Kiname/vapemacerator-mk1/SolidWorks/flame.jpg

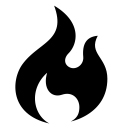
SolidWorks/flame.jpg
