Kiname/vapemacerator-mk1/SolidWorks/soporte-50ml-35mm.SLDPRT

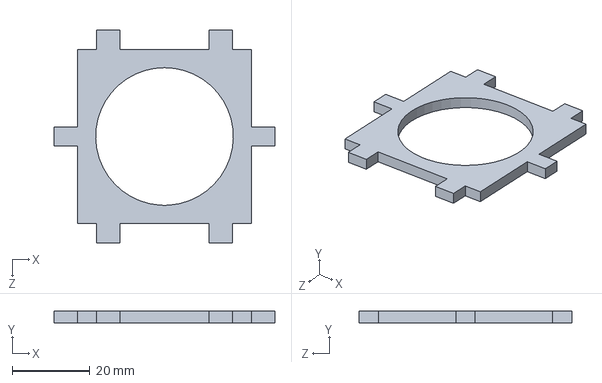
[picture p18: CAD file, 2015-08-10]
SolidWorks/soporte-50ml-35mm.SLDPRT
57.0 x 3.00 x 55.0 mm
