Kiname/vapemacerator-mk1/SolidWorks/base-back.SLDPRT

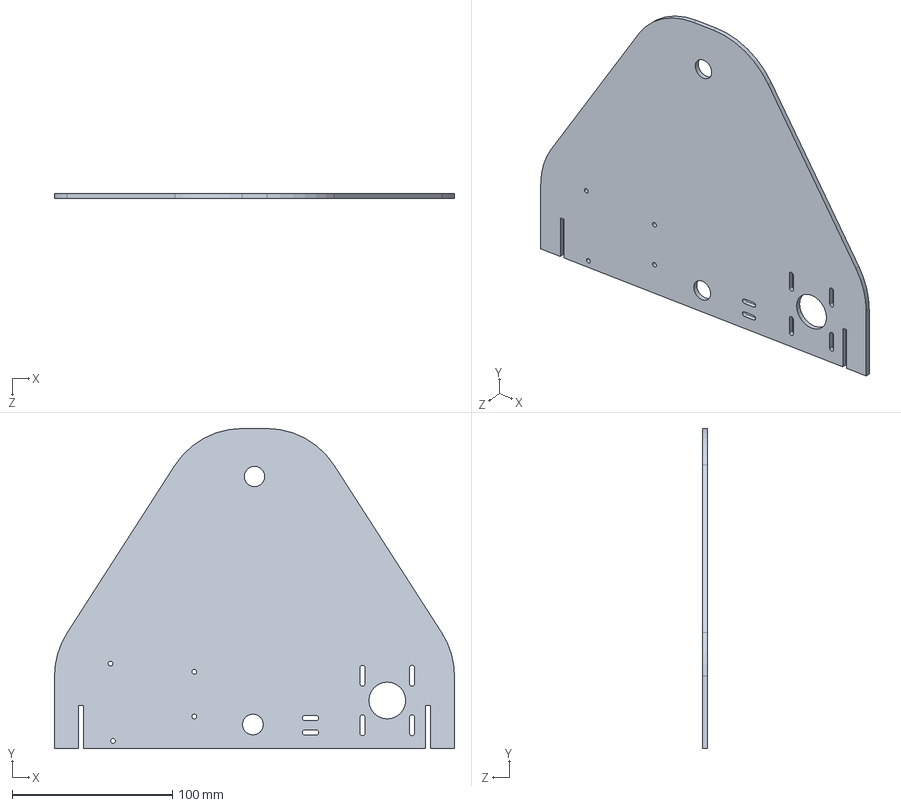
[picture p19: CAD file, 2015-08-10]
SolidWorks/base-back.SLDPRT
250.0 x 200.0 x 3.00 mm
