Kiname/vapemacerator-mk1/SolidWorks/acople.SLDPRT

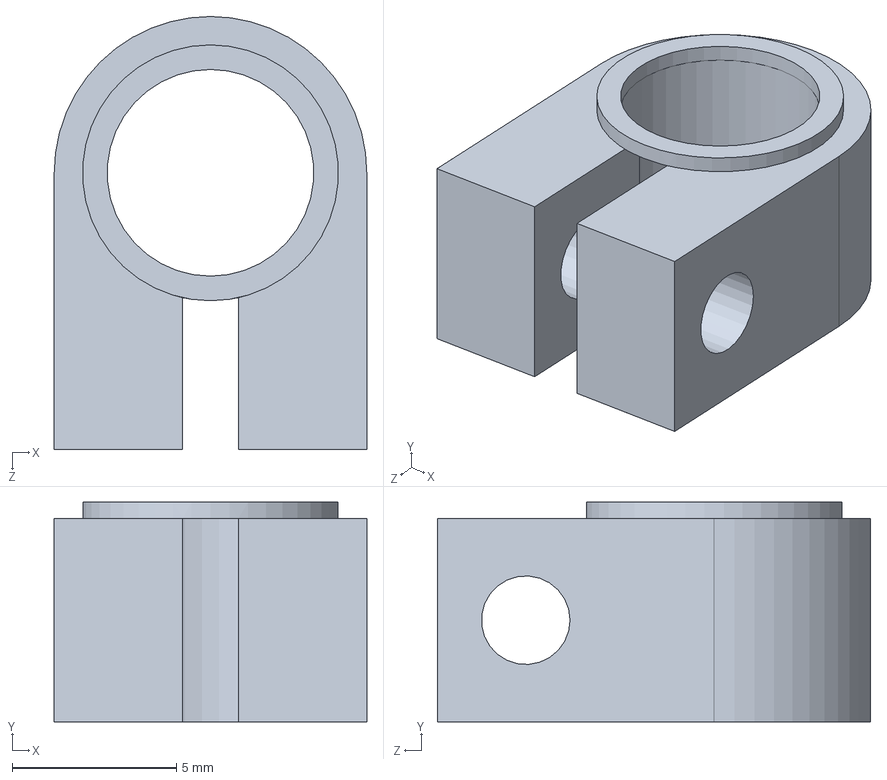
[picture p20: CAD file, 2015-08-10]
SolidWorks/acople.SLDPRT
9.53 x 6.70 x 13.2 mm
