Kiname/vapemacerator-mk1/SolidWorks/serial-lcd.SLDPRT

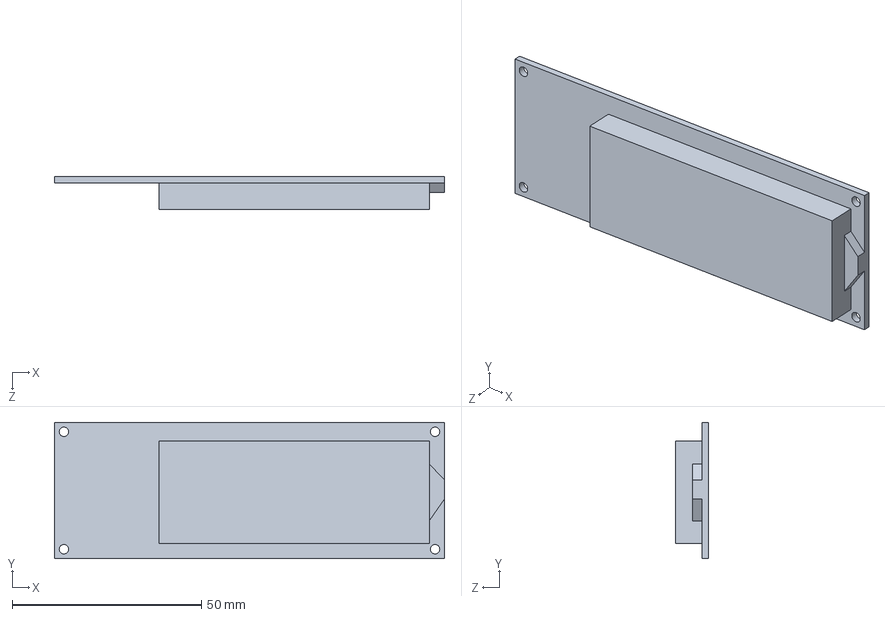
[picture p21: CAD file, 2015-08-10]
SolidWorks/serial-lcd.SLDPRT
103.0 x 36.0 x 8.75 mm
