Kiname/vapemacerator-mk1/SolidWorks/stepper-motor.sldprt

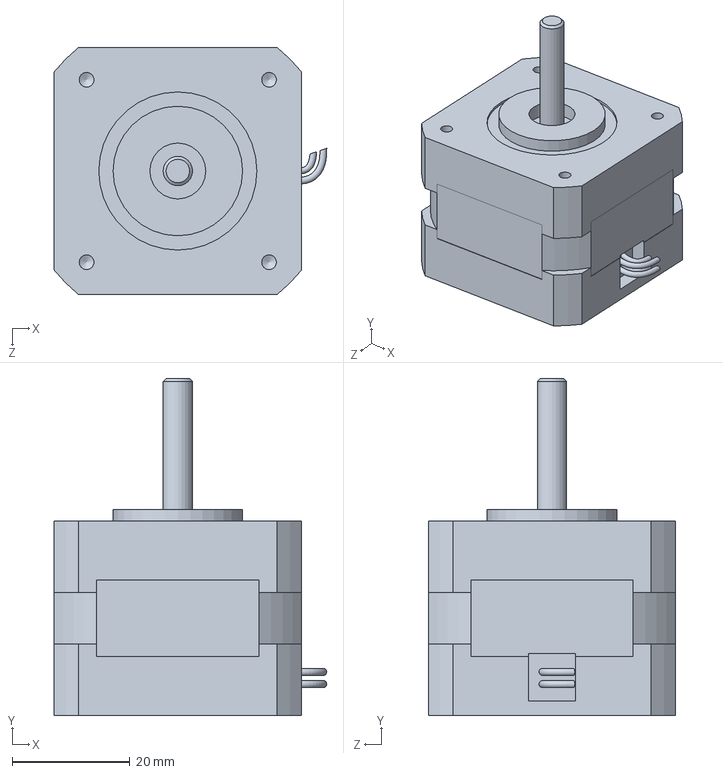
[picture p22: CAD file, 2015-08-10]
SolidWorks/stepper-motor.sldprt
46.3 x 57.2 x 42.0 mm
