Kiname/vapemacerator-mk1/SolidWorks/bote-50ml.SLDPRT

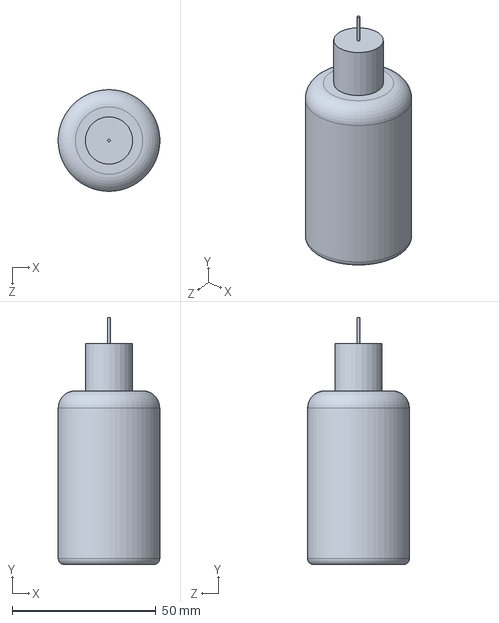
[picture p23: CAD file, 2015-08-10]
SolidWorks/bote-50ml.SLDPRT
35.3 x 85.9 x 35.4 mm
