Kiname/vapemacerator-mk1/SolidWorks/Arduino UNO.SLDPRT

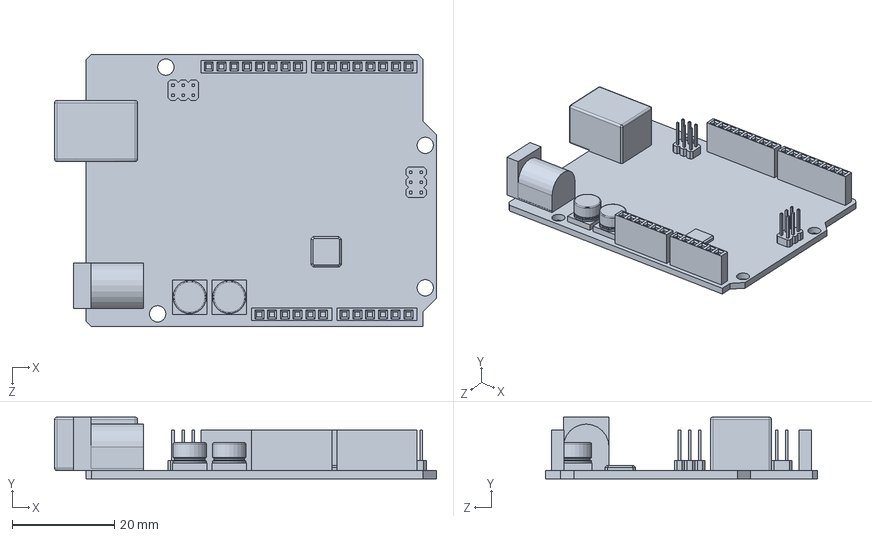
[picture p24: CAD file, 2015-08-10]
SolidWorks/Arduino UNO.SLDPRT
74.8 x 12.1 x 53.3 mm
