Kiname/vapemacerator-mk1/SolidWorks/separador-metal.SLDPRT

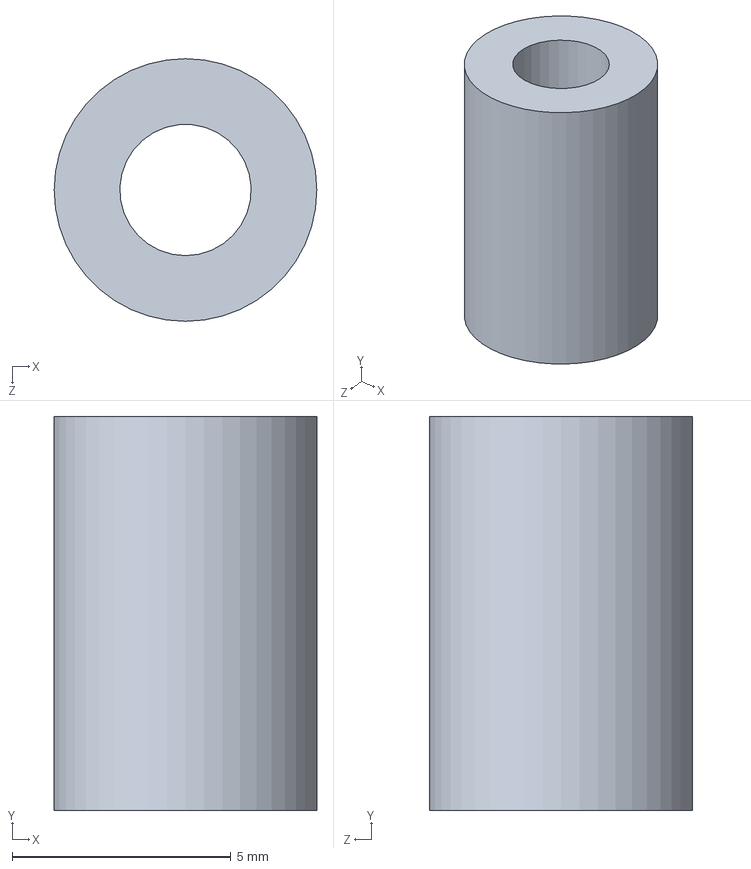
[picture p25: CAD file, 2015-08-10]
SolidWorks/separador-metal.SLDPRT
6.00 x 9.00 x 6.00 mm
